0x0c/spltnrskb/docs/img/dial-study/dial-grid.jpg

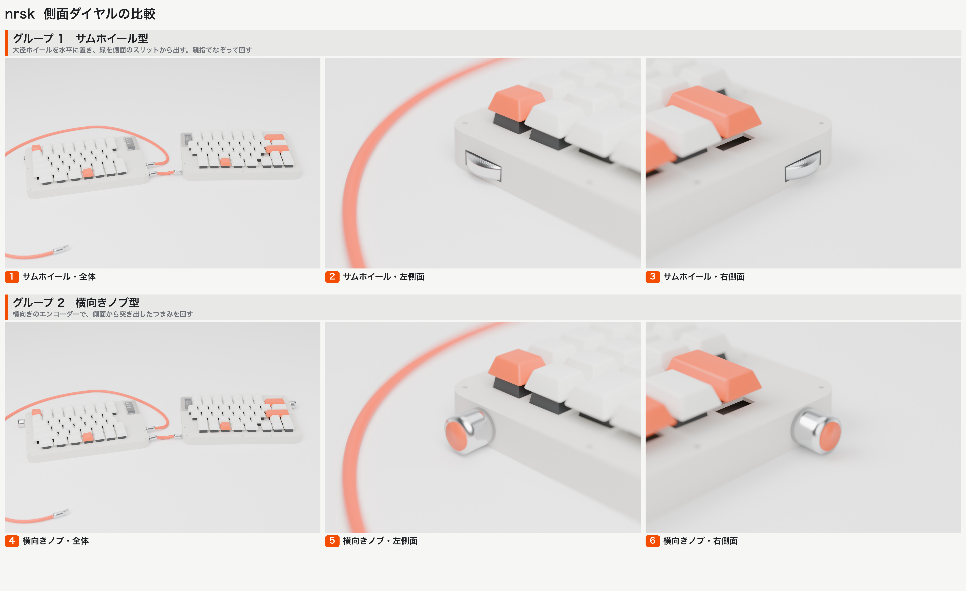
docs/img/dial-study/dial-grid.jpg
