0x0c/spltnrskb/docs/img/dial-study/dial-left-knob.png

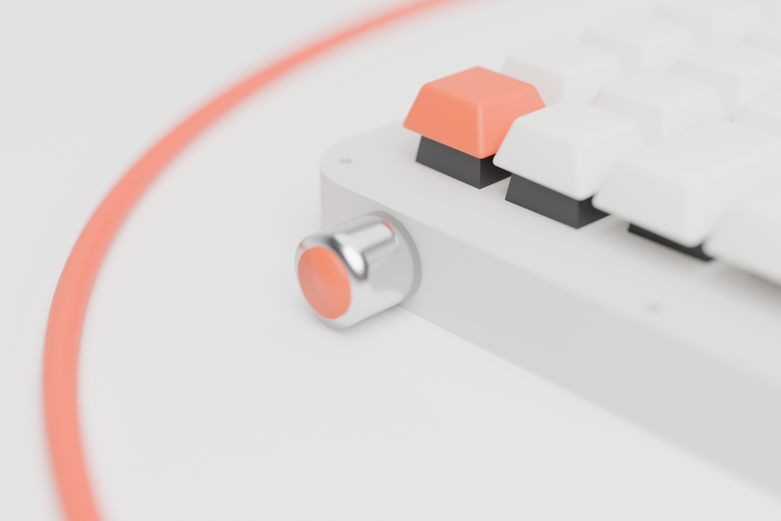
docs/img/dial-study/dial-left-knob.png
