0x0c/spltnrskb/docs/img/dial-study/dial-right-knob.png

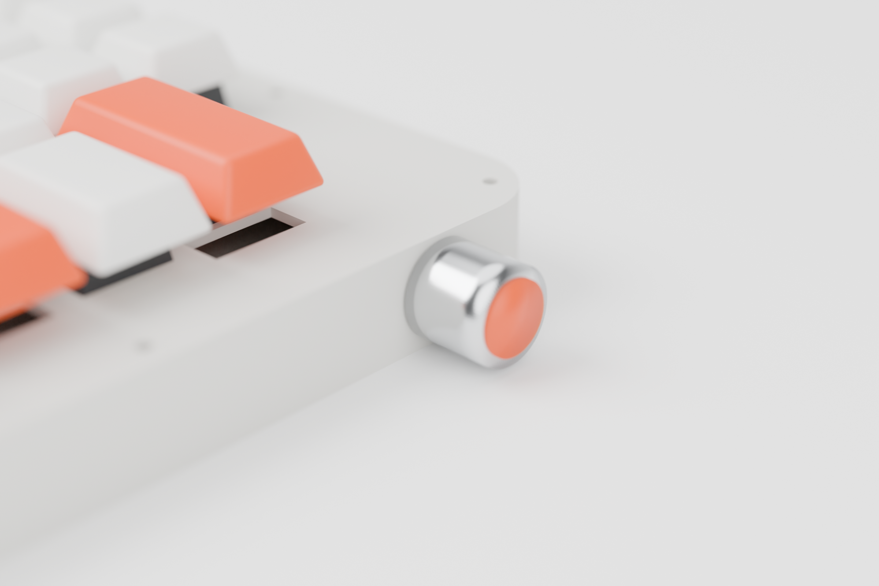
docs/img/dial-study/dial-right-knob.png
