0x0c/spltnrskb/docs/img/dial-study/hero-knob.png

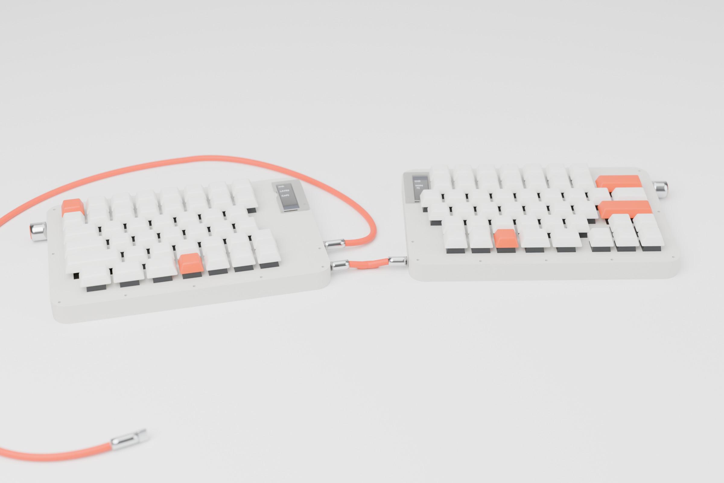
docs/img/dial-study/hero-knob.png
