0x0c/spltnrskb/docs/img/encoder-study/exploded-left.png

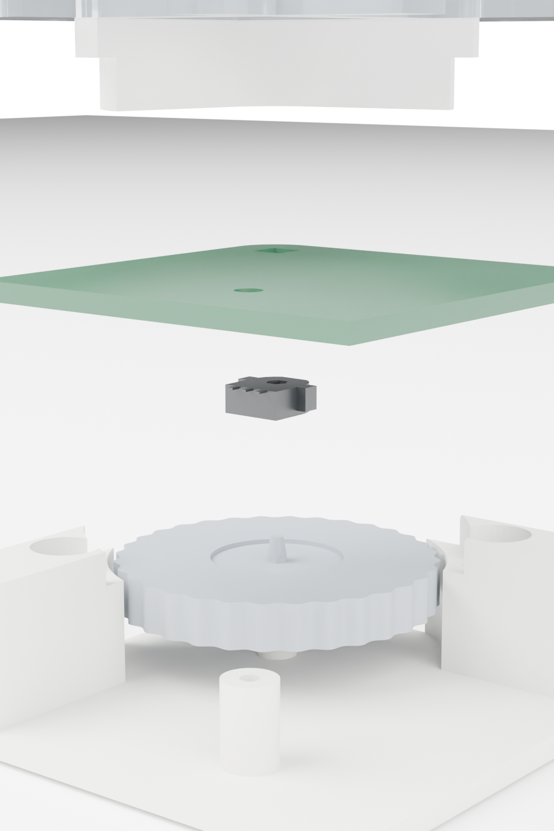
docs/img/encoder-study/exploded-left.png
