0x0c/spltnrskb/docs/img/encoder-study/exterior-right.png

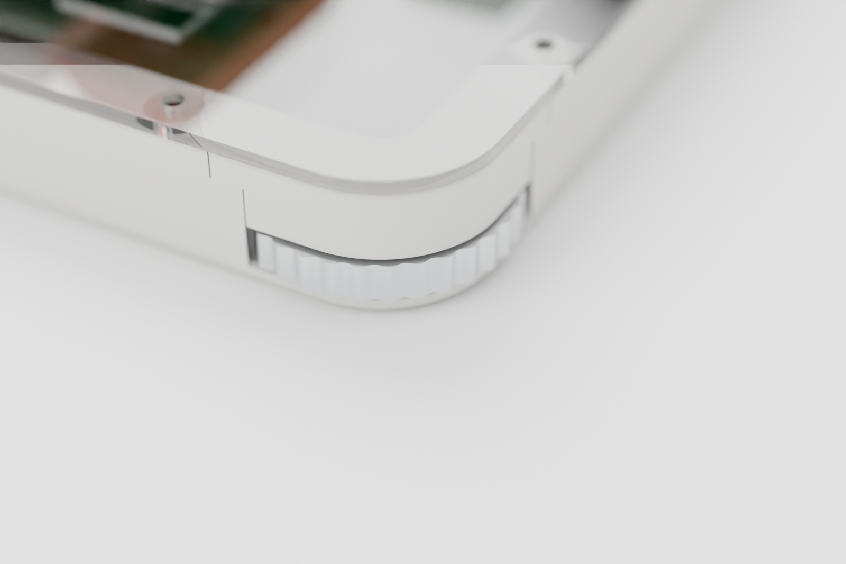
docs/img/encoder-study/exterior-right.png
