0x0c/spltnrskb/docs/img/encoder-study/section-left-encoder.png

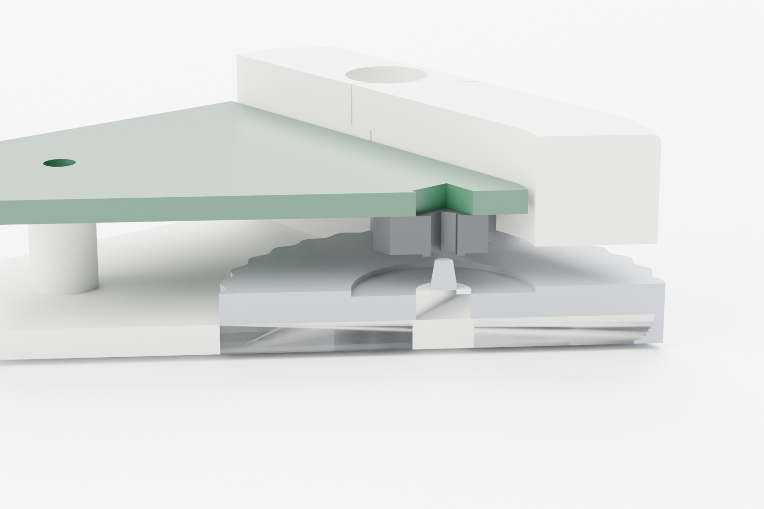
docs/img/encoder-study/section-left-encoder.png
