0x0c/spltnrskb/docs/img/oled-study/close-0.png

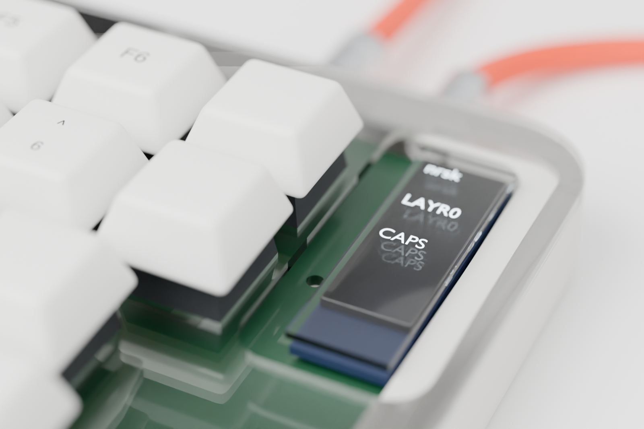
docs/img/oled-study/close-0.png
