0x0c/spltnrskb/docs/img/oled-study/close-3.5.png

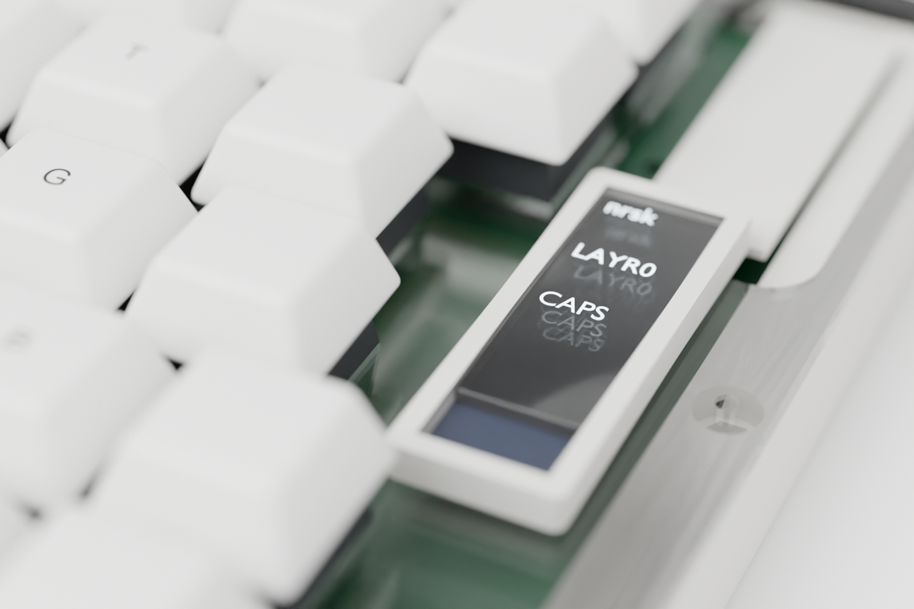
docs/img/oled-study/close-3.5.png
