0x0c/spltnrskb/docs/img/oled-study/close-13.png

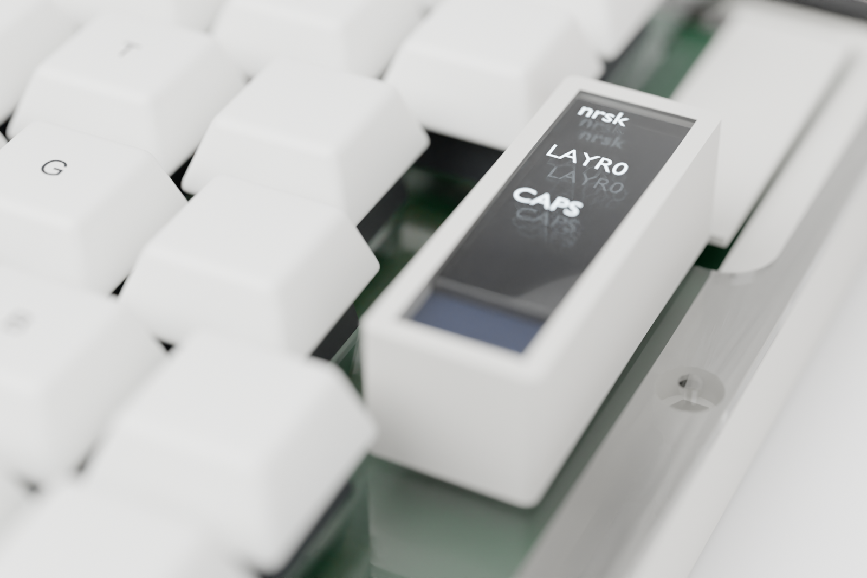
docs/img/oled-study/close-13.png
