0x0c/spltnrskb/docs/img/oled-study/close-tilt-h.png

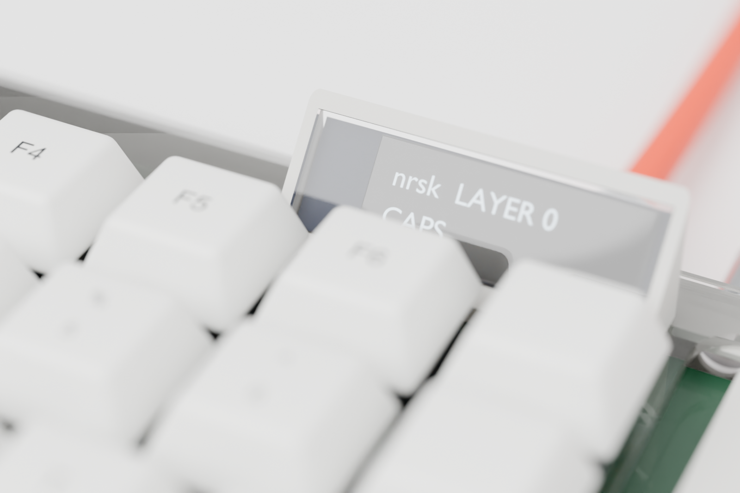
docs/img/oled-study/close-tilt-h.png
