0x0c/spltnrskb/docs/img/oled-study/close-tilt-v.png

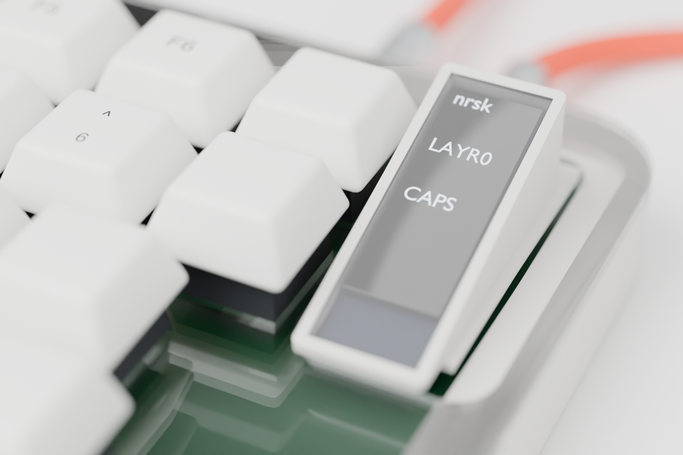
docs/img/oled-study/close-tilt-v.png
