0x0c/spltnrskb/docs/img/oled-study/user-0.png

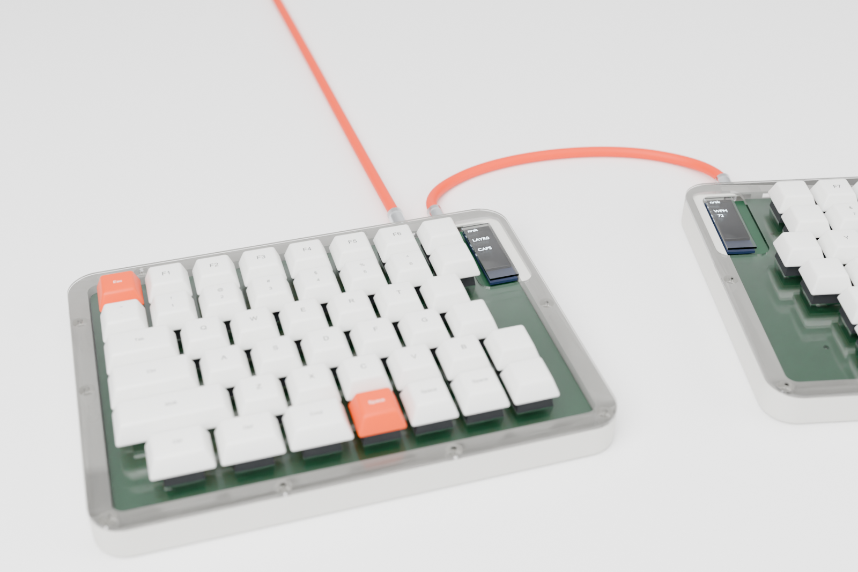
docs/img/oled-study/user-0.png
