0x0c/spltnrskb/docs/img/oled-study/user-tilt-h.png

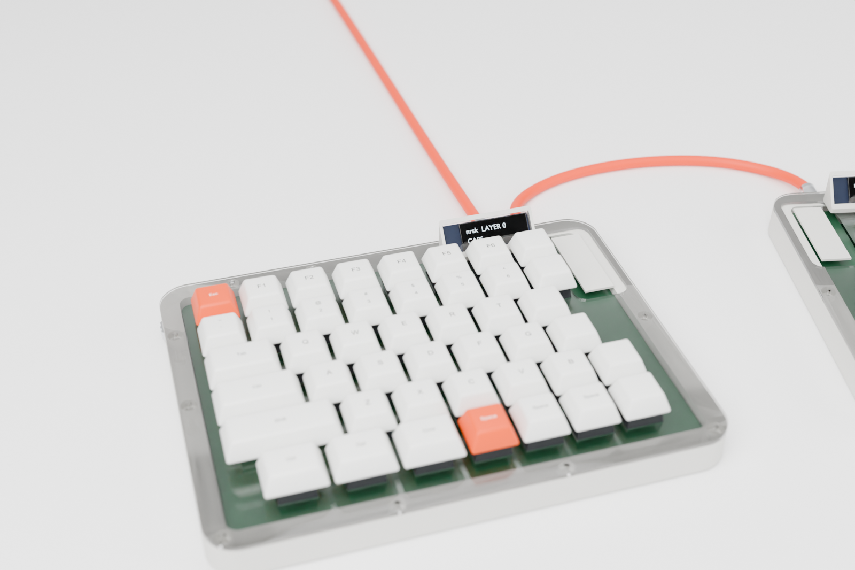
docs/img/oled-study/user-tilt-h.png
