0x0c/spltnrskb/docs/img/oled-study/user-tilt-v.png

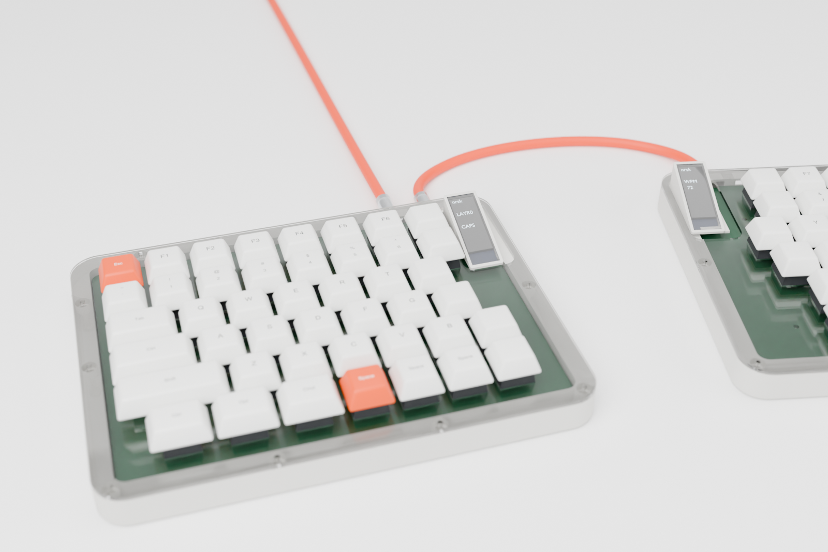
docs/img/oled-study/user-tilt-v.png
