0x0c/spltnrskb/docs/img/ports-compare.jpg

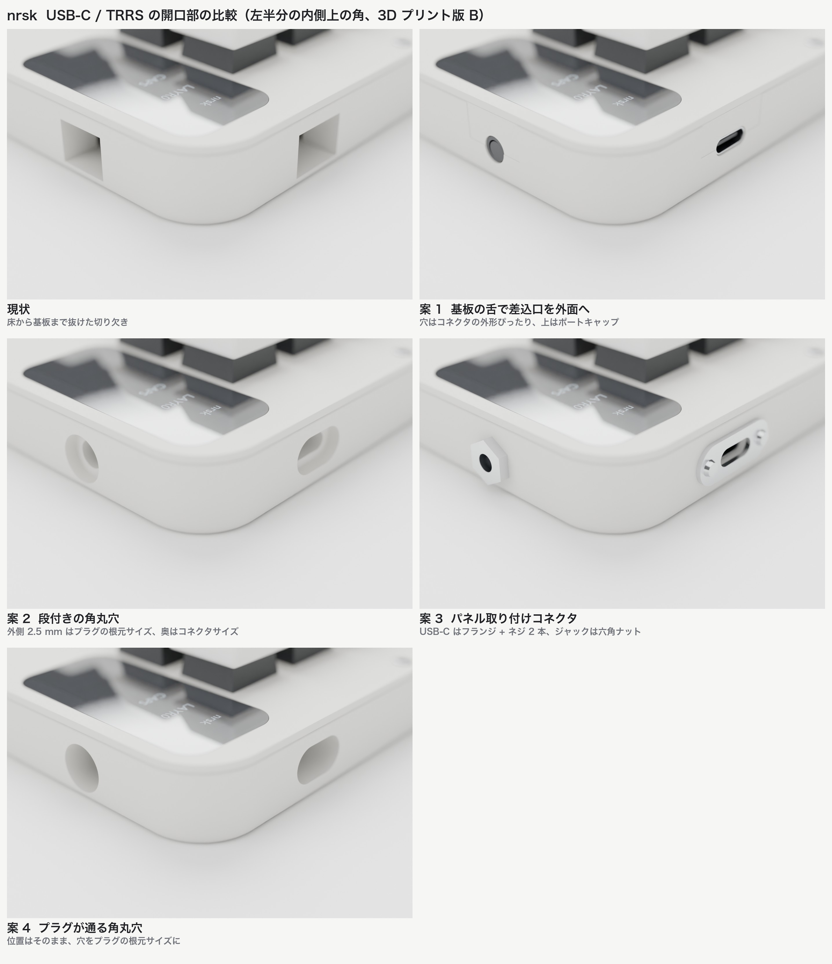
docs/img/ports-compare.jpg
