0x0c/spltnrskb/docs/img/render-detail.png

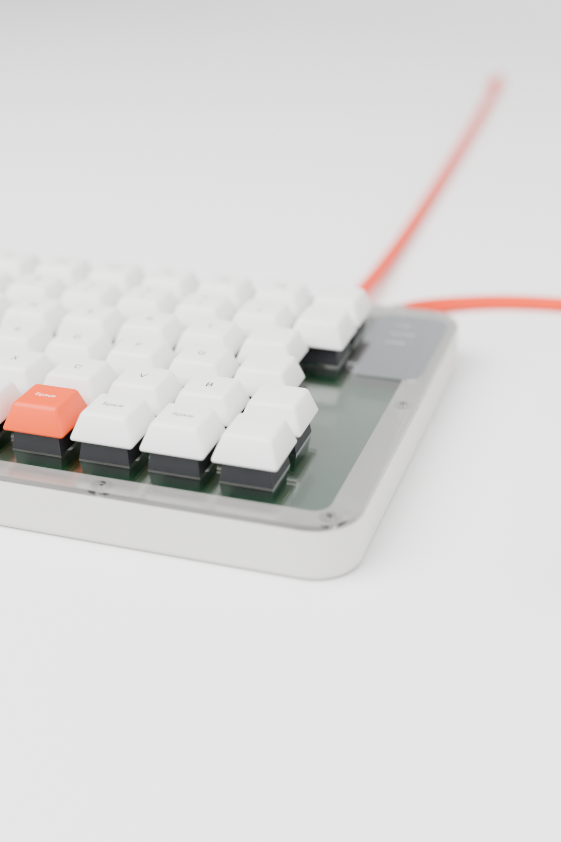
docs/img/render-detail.png
