0x0c/spltnrskb/docs/img/render-grid.jpg

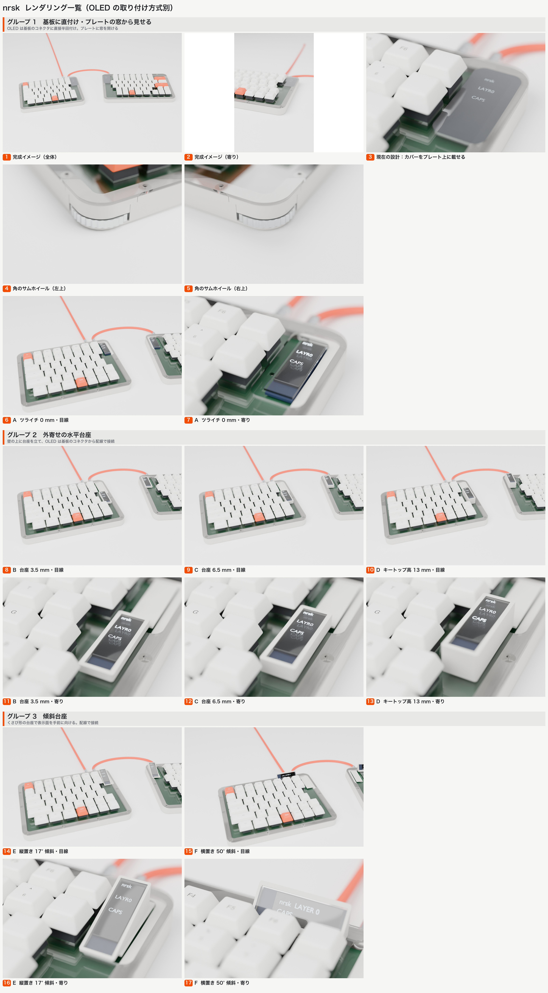
docs/img/render-grid.jpg
