0x0c/spltnrskb/docs/img/render-hero-top-acrylic-flat.png

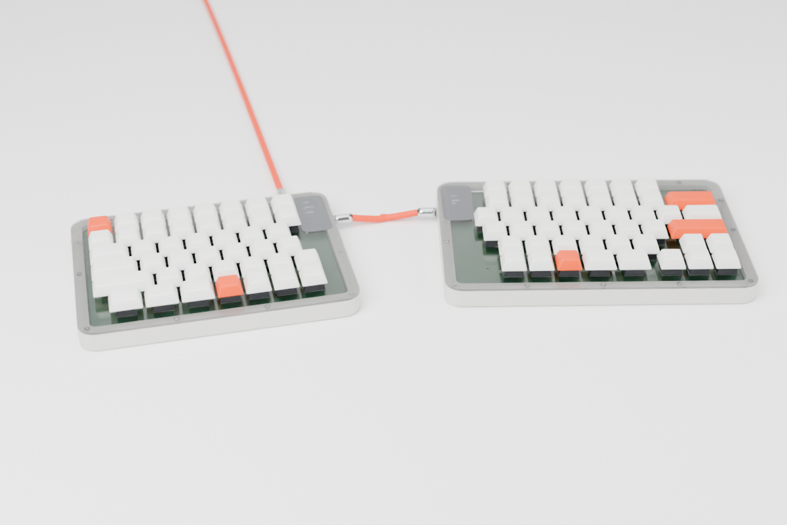
docs/img/render-hero-top-acrylic-flat.png
