0x0c/spltnrskb/docs/img/render-oled-top-acrylic-flat.png

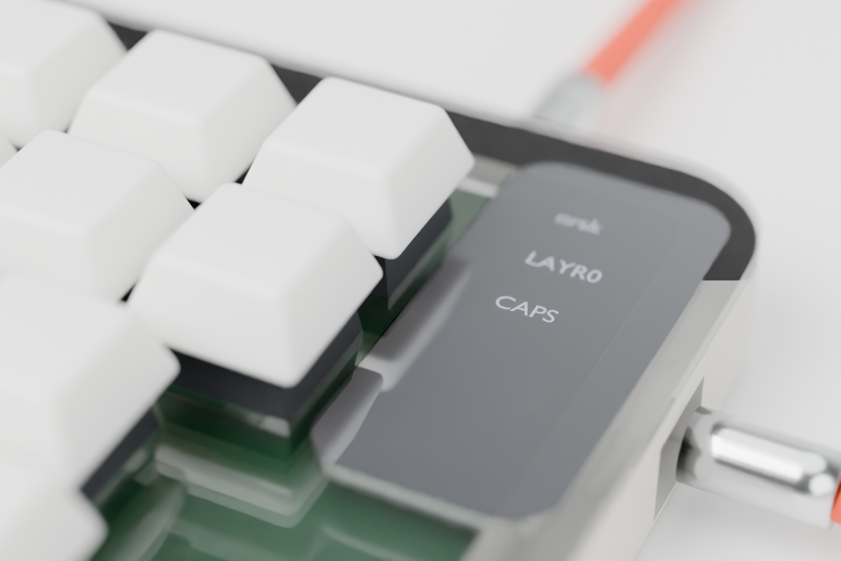
docs/img/render-oled-top-acrylic-flat.png
