0x0c/spltnrskb/docs/img/render-oled-top-acrylic-lowpan.png

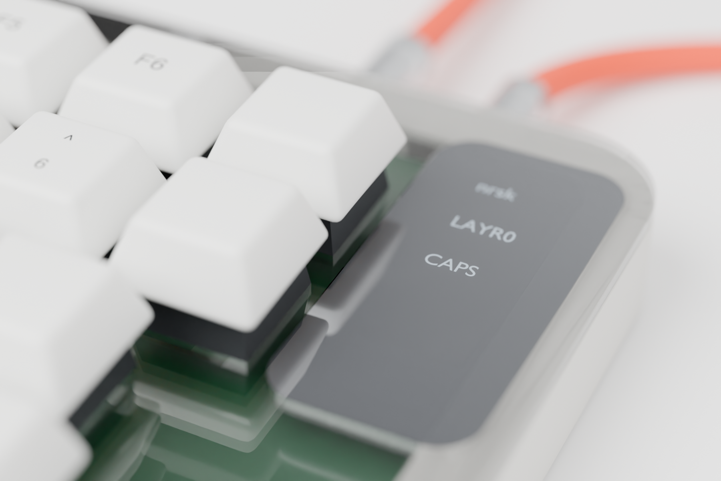
docs/img/render-oled-top-acrylic-lowpan.png
