0x0c/spltnrskb/docs/img/render-ports-current.png

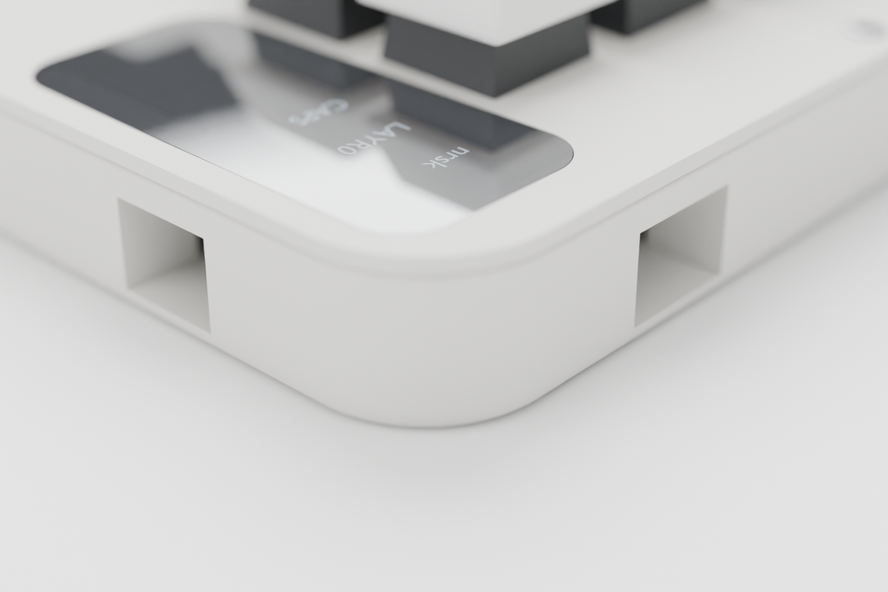
docs/img/render-ports-current.png
