0x0c/spltnrskb/docs/img/right-case-overlay.png

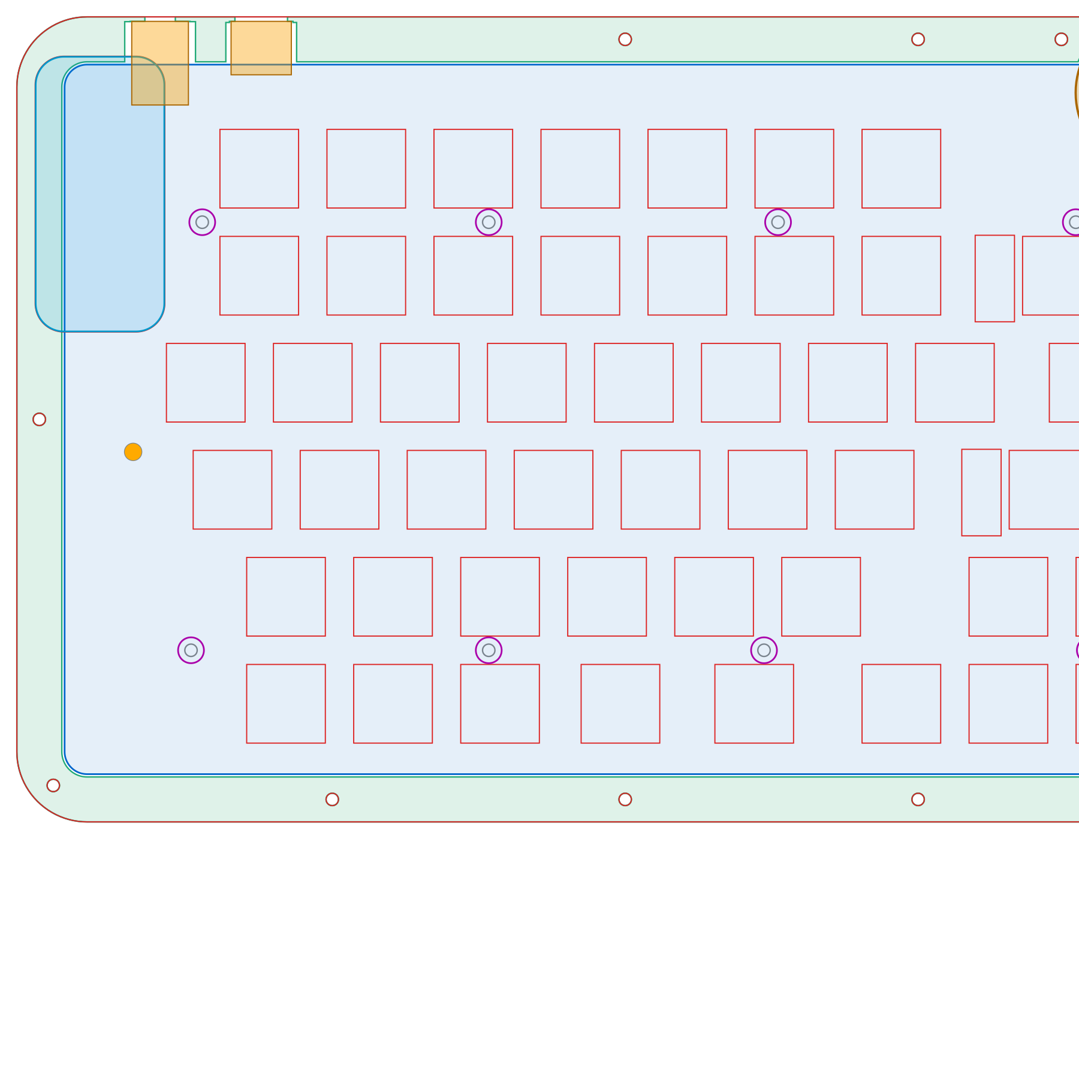
docs/img/right-case-overlay.png
