0x0c/spltnrskb/case/laser/left-frame3.dxf

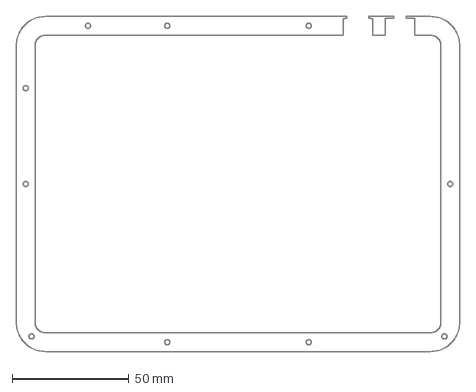
[picture p52: CAD file, 2026-10-10]
case/laser/left-frame3.dxf
189.6 x 143.3 mm
