0x0c/spltnrskb/case/preview/oled-variants/right-lens-tilt-h.stl

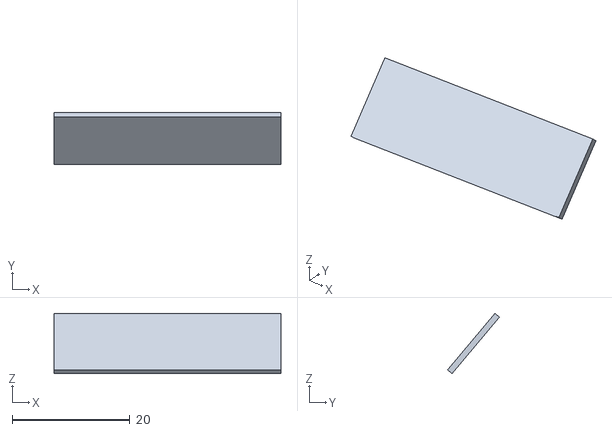
[picture p53: CAD file, 2026-10-04]
case/preview/oled-variants/right-lens-tilt-h.stl
38.5 x 8.80 x 10.2
