0x0c/spltnrskb/case/preview/port-variants/left-panel-heads.stl

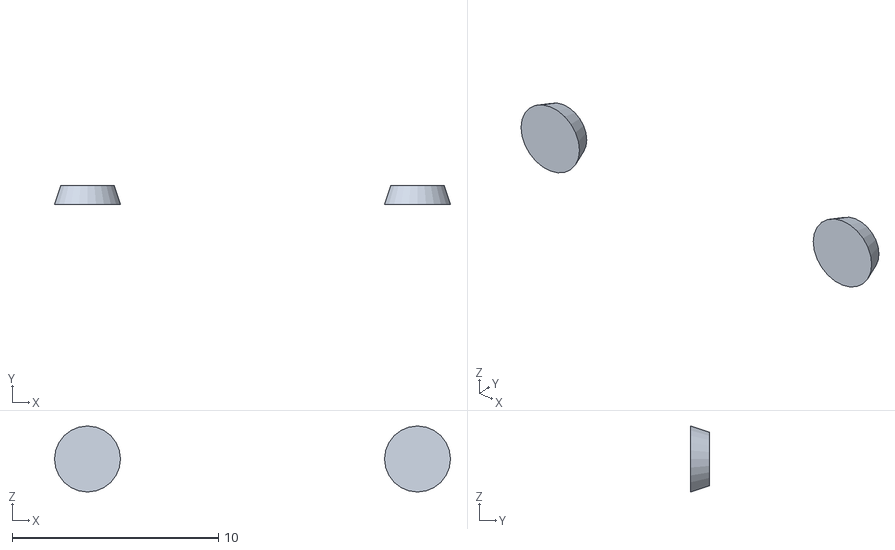
[picture p54: CAD file, 2026-10-05]
case/preview/port-variants/left-panel-heads.stl
19.2 x 0.9 x 3.20
