0x0c/spltnrskb/case/preview/right-pcb.stl

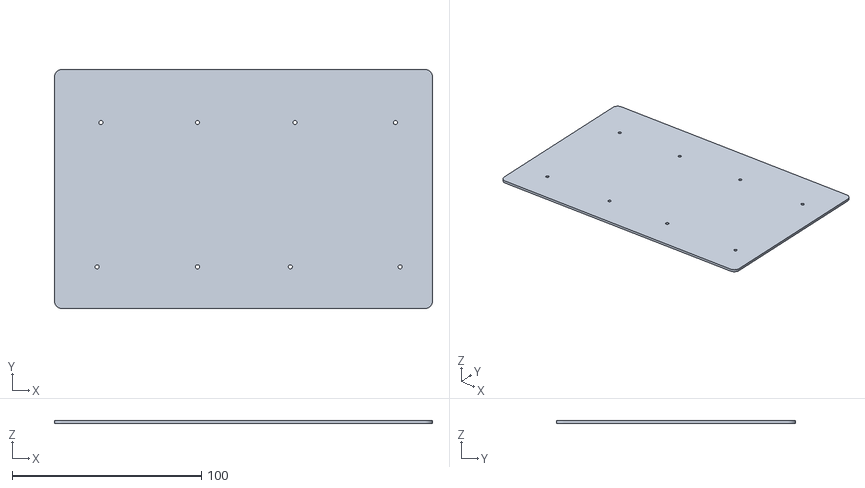
[picture p55: CAD file, 2026-10-10]
case/preview/right-pcb.stl
199.6 x 126.3 x 1.60
