0x0c/spltnrskb/case/print/left-tray.stl

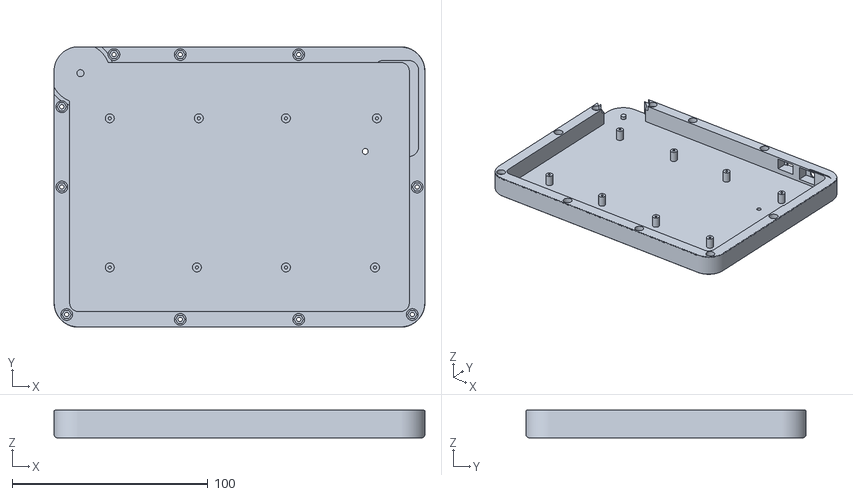
[picture p56: CAD file, 2026-10-10]
case/print/left-tray.stl
189.6 x 143.3 x 14.1
