0x0c/spltnrskb/case/laser/left-frame2.dxf

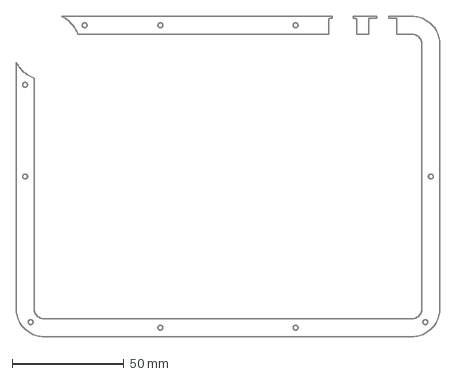
[picture p57: CAD file, 2026-10-10]
case/laser/left-frame2.dxf
189.6 x 143.3 mm
