0x0c/spltnrskb/case/preview/left-oled-cover.stl

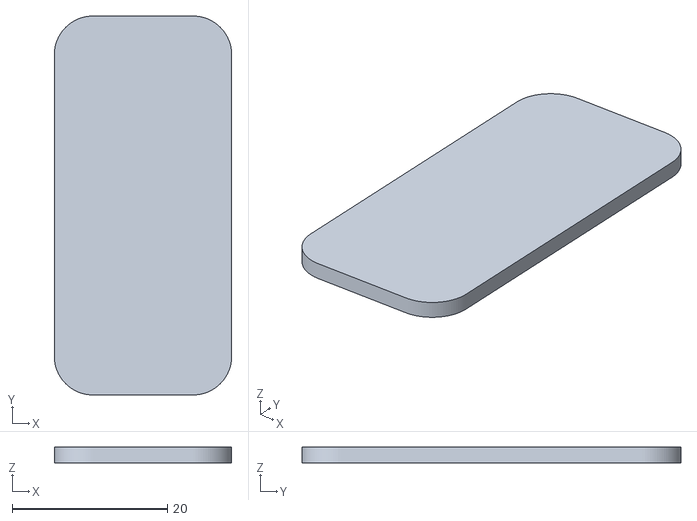
[picture p58: CAD file, 2026-10-05]
case/preview/left-oled-cover.stl
22.9 x 48.9 x 2.00
