0x0c/spltnrskb/case/preview/oled-variants/left-lens-tilt-v.stl

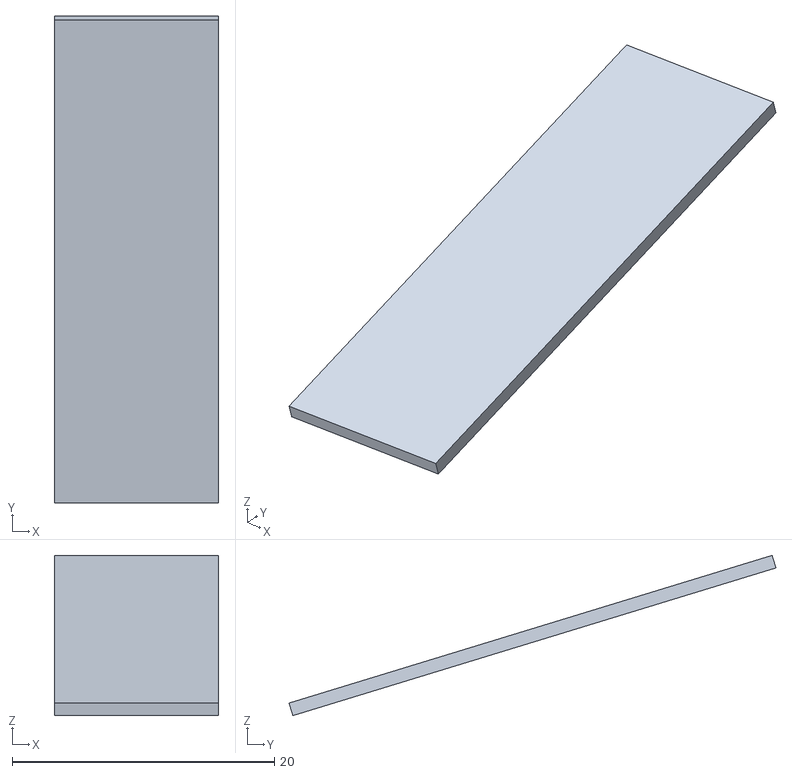
[picture p59: CAD file, 2026-10-04]
case/preview/oled-variants/left-lens-tilt-v.stl
12.5 x 37.1 x 12.2
