0x0c/spltnrskb/case/print/right-plate.stl

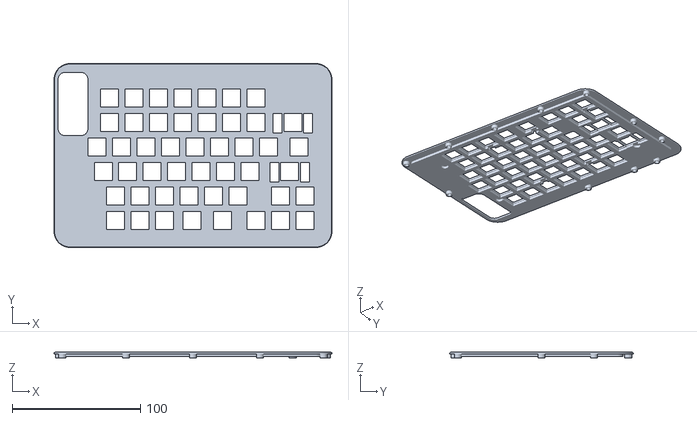
[picture p60: CAD file, 2026-10-10]
case/print/right-plate.stl
216.6 x 143.3 x 4.50
