0x0c/spltnrskb/case/laser/right-plate.dxf

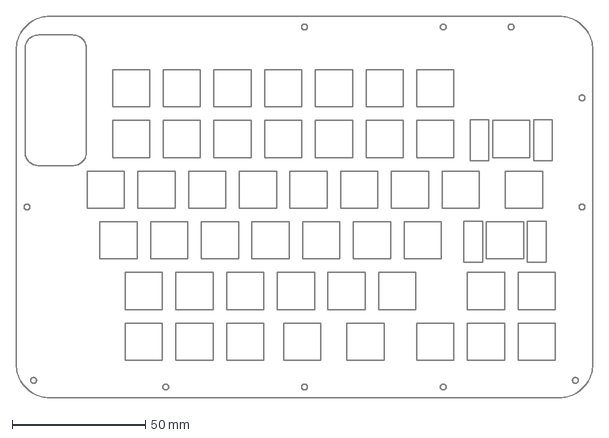
[picture p61: CAD file, 2026-10-10]
case/laser/right-plate.dxf
216.6 x 143.3 mm
