0x0c/spltnrskb/case/preview/oled-variants/left-lens-13.stl

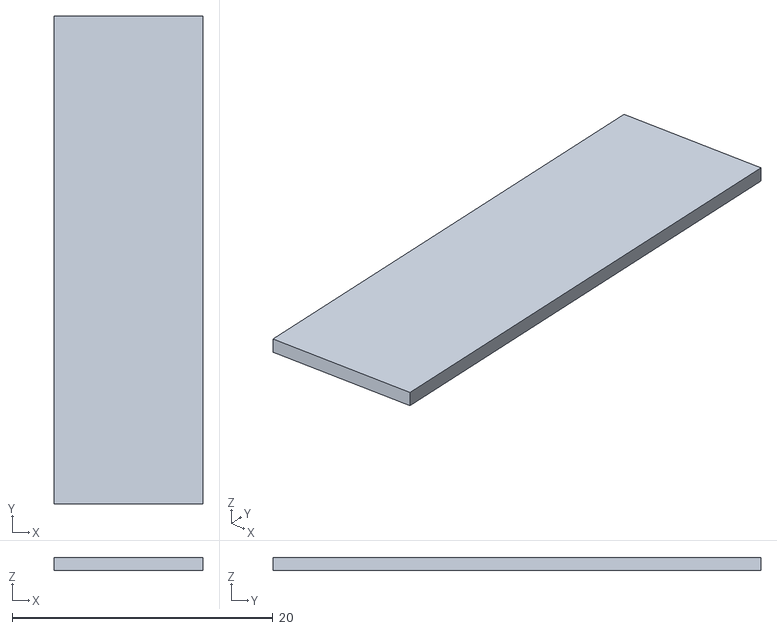
[picture p62: CAD file, 2026-10-04]
case/preview/oled-variants/left-lens-13.stl
11.4 x 37.4 x 1.00
