0x0c/spltnrskb/case/laser/left-frame1.dxf

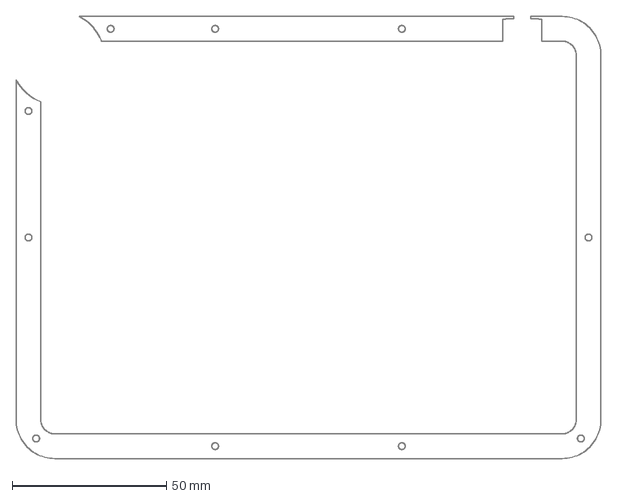
[picture p63: CAD file, 2026-10-10]
case/laser/left-frame1.dxf
189.6 x 143.3 mm
