0x0c/spltnrskb/case/preview/oled-variants/left-pod-6.5.stl

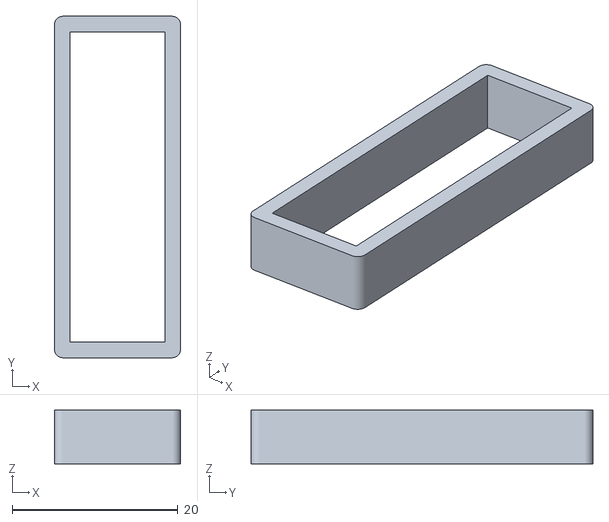
[picture p64: CAD file, 2026-10-04]
case/preview/oled-variants/left-pod-6.5.stl
15.2 x 41.2 x 6.50
