0x0c/spltnrskb/case/preview/port-variants/left-flush-jack.stl

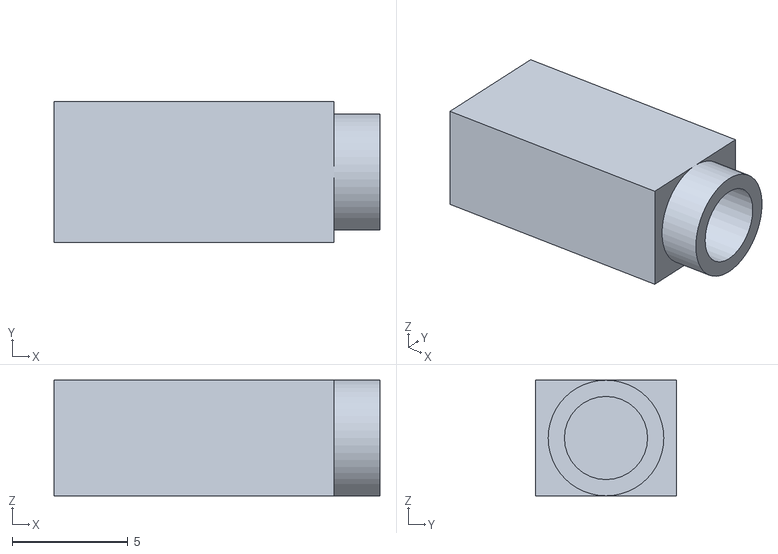
[picture p65: CAD file, 2026-10-05]
case/preview/port-variants/left-flush-jack.stl
14.1 x 6.10 x 5.00
