0x0c/spltnrskb/case/laser/left-bottom.dxf

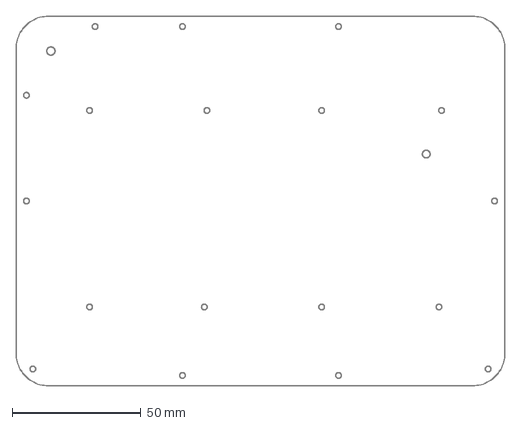
[picture p66: CAD file, 2026-10-10]
case/laser/left-bottom.dxf
189.6 x 143.3 mm
