0x0c/spltnrskb/case/preview/port-variants/left-flush-bore.stl

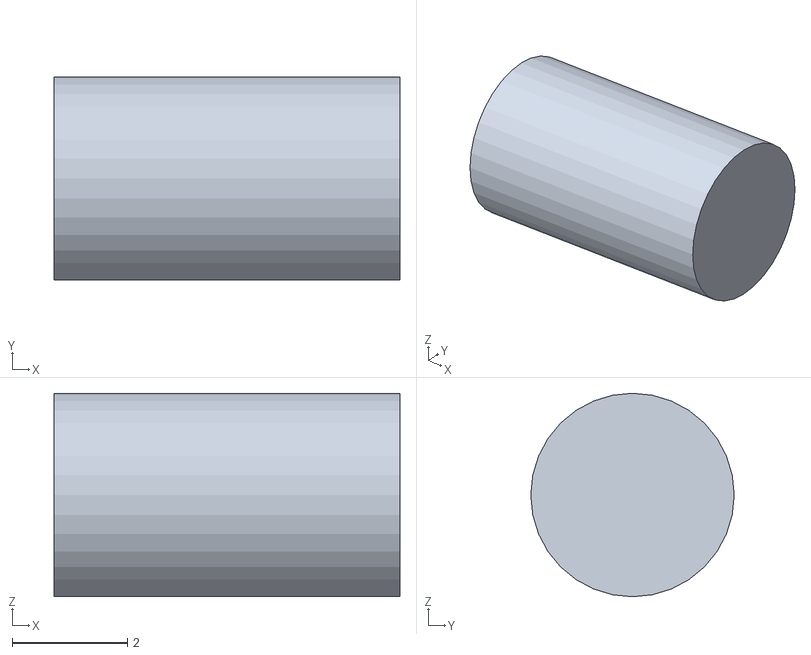
[picture p67: CAD file, 2026-10-05]
case/preview/port-variants/left-flush-bore.stl
6.00 x 3.53 x 3.53
