0x0c/spltnrskb/case/print/left-plate.stl

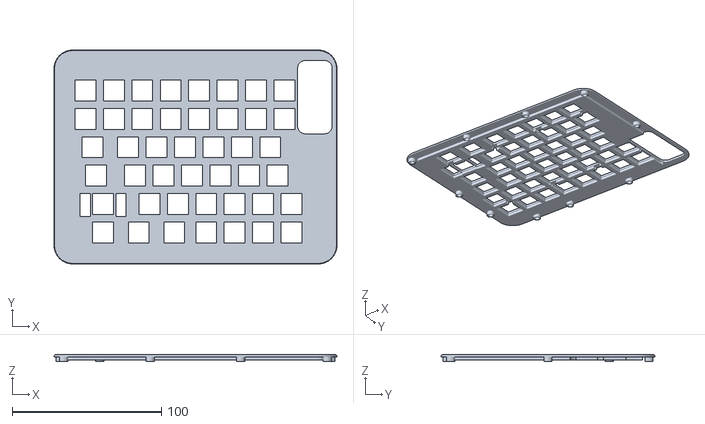
[picture p68: CAD file, 2026-10-10]
case/print/left-plate.stl
189.6 x 143.3 x 4.50
