0x0c/spltnrskb/case/laser/left-plate.dxf

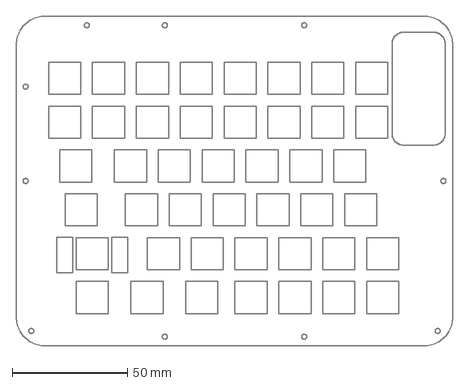
[picture p69: CAD file, 2026-10-10]
case/laser/left-plate.dxf
189.6 x 143.3 mm
