0x0c/spltnrskb/case/preview/port-variants/left-flush-shell.stl

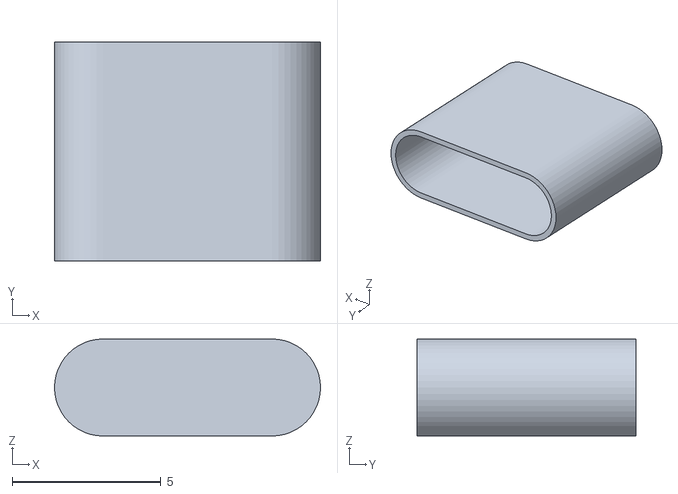
[picture p70: CAD file, 2026-10-05]
case/preview/port-variants/left-flush-shell.stl
8.94 x 7.35 x 3.26
