0x0c/spltnrskb/case/print/pin-coupon.stl

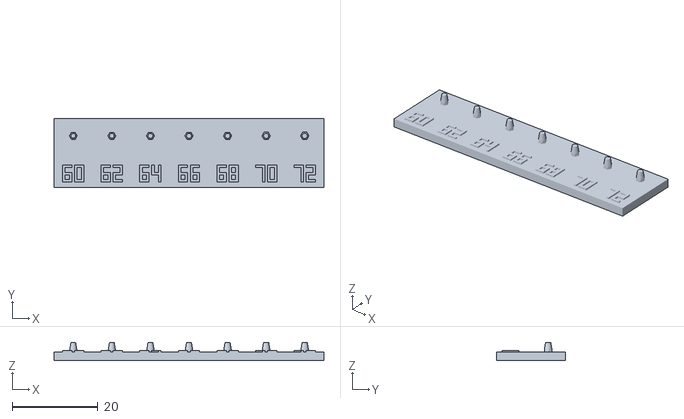
[picture p71: CAD file, 2026-10-10]
case/print/pin-coupon.stl
63.0 x 16.0 x 4.30
