0x0c/spltnrskb/case/laser/right-frame2.dxf

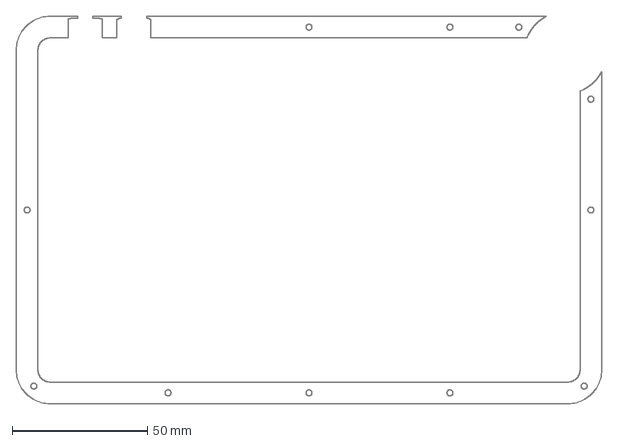
[picture p72: CAD file, 2026-10-10]
case/laser/right-frame2.dxf
216.6 x 143.3 mm
