0x0c/spltnrskb/case/laser/right-frame4.dxf

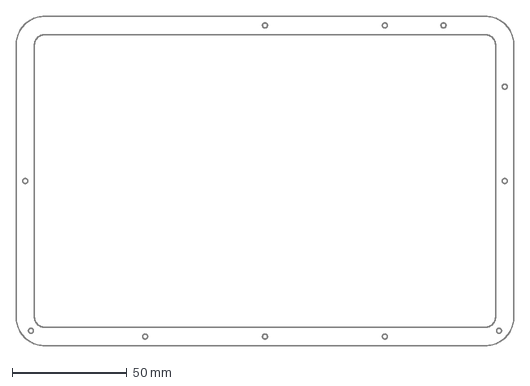
[picture p73: CAD file, 2026-10-10]
case/laser/right-frame4.dxf
216.6 x 143.3 mm
