0x0c/spltnrskb/case/preview/oled-variants/right-pod-tilt-h.stl

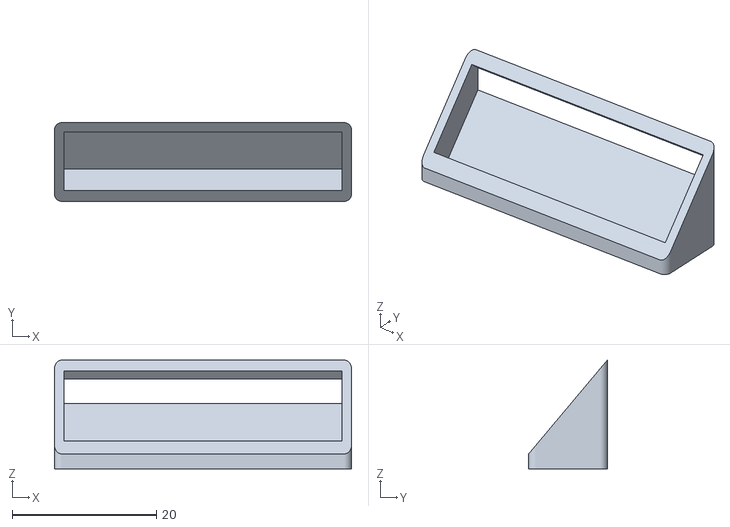
[picture p74: CAD file, 2026-10-04]
case/preview/oled-variants/right-pod-tilt-h.stl
41.2 x 10.9 x 15.1
