0x0c/spltnrskb/case/laser/right-frame1.dxf

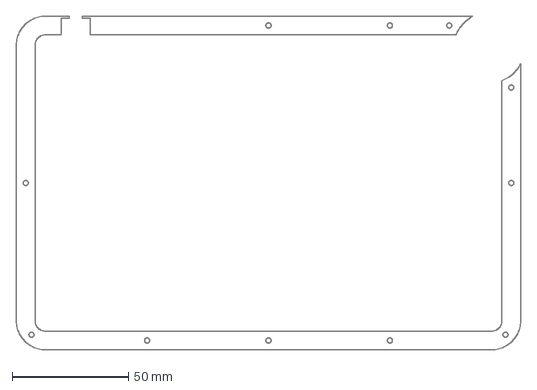
[picture p75: CAD file, 2026-10-10]
case/laser/right-frame1.dxf
216.6 x 143.3 mm
