0x0c/spltnrskb/case/laser/right-oled-cover.dxf

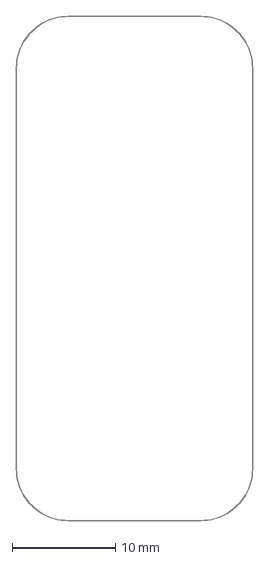
[picture p76: CAD file, 2026-10-05]
case/laser/right-oled-cover.dxf
22.9 x 48.9 mm
