0x0c/spltnrskb/case/preview/oled-variants/right-pod-tilt-v.stl

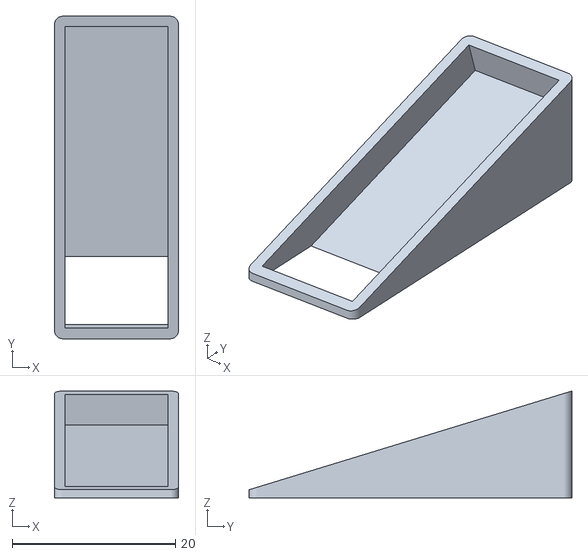
[picture p77: CAD file, 2026-10-04]
case/preview/oled-variants/right-pod-tilt-v.stl
15.2 x 39.5 x 13.1
