0x0c/spltnrskb/case/laser/left-oled-cover.dxf

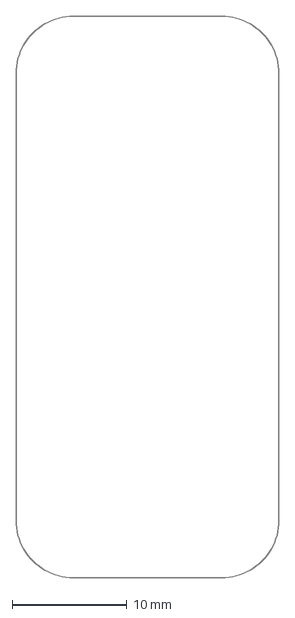
[picture p78: CAD file, 2026-10-05]
case/laser/left-oled-cover.dxf
22.9 x 48.9 mm
