0x0c/spltnrskb/case/preview/oled-variants/right-pod-3.5.stl

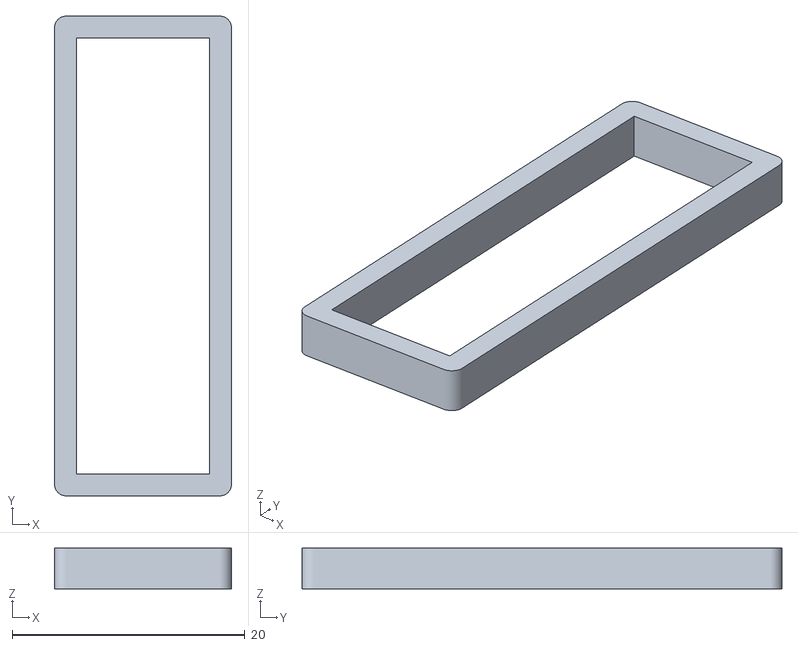
[picture p79: CAD file, 2026-10-04]
case/preview/oled-variants/right-pod-3.5.stl
15.2 x 41.2 x 3.50
