0x0c/spltnrskb/case/preview/port-variants/left-flush-cap.stl

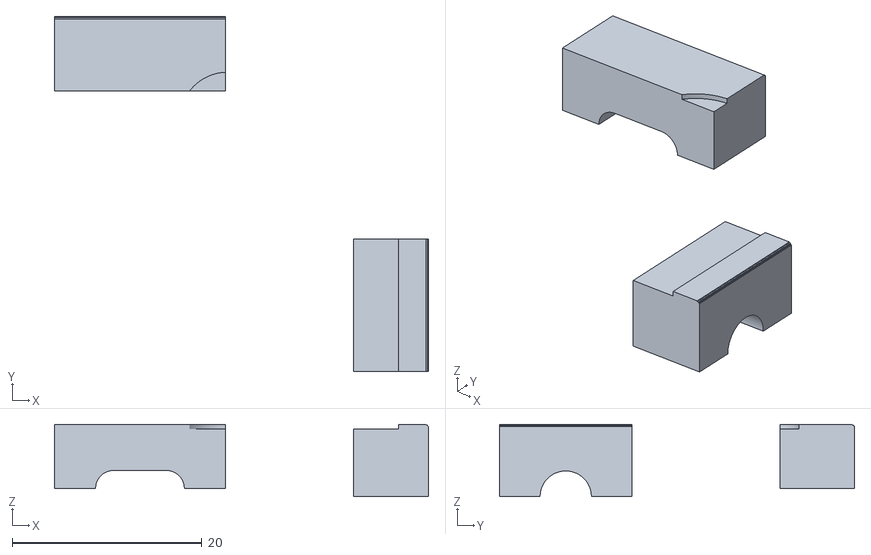
[picture p80: CAD file, 2026-10-05]
case/preview/port-variants/left-flush-cap.stl
39.4 x 37.4 x 7.60
