0x0c/spltnrskb/case/preview/port-variants/left-panel-tongue.stl

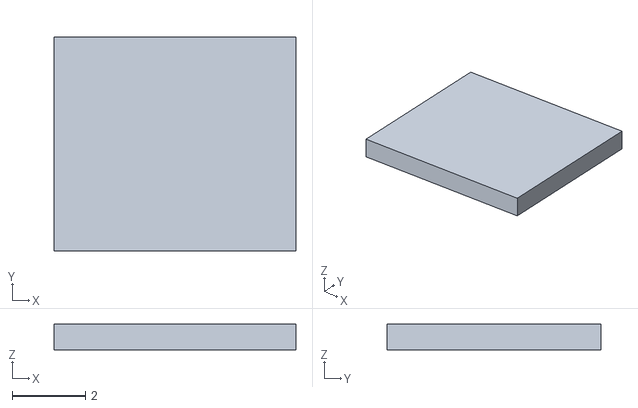
[picture p81: CAD file, 2026-10-05]
case/preview/port-variants/left-panel-tongue.stl
6.60 x 5.85 x 0.7
