0x0c/spltnrskb/docs/img/render-oled-top-print.png

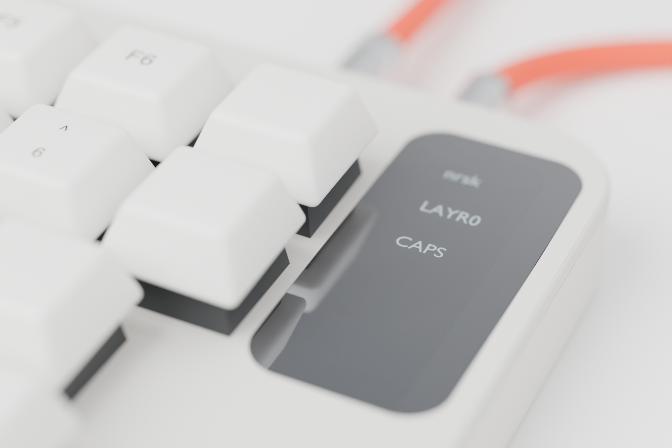
docs/img/render-oled-top-print.png
