0x0c/spltnrskb/docs/img/render-wheel-left-top-print-flat.png

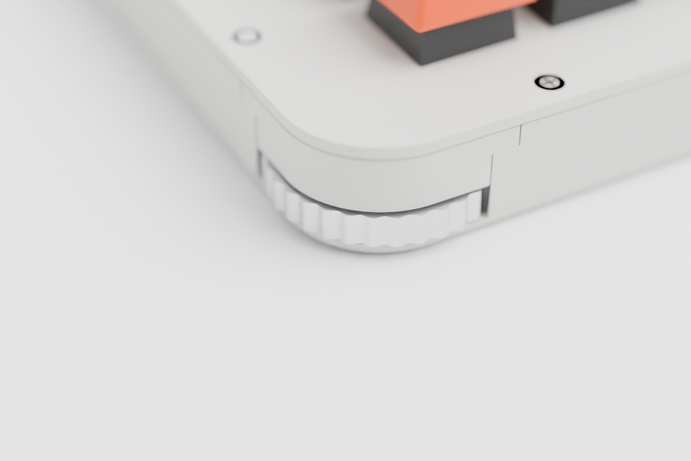
docs/img/render-wheel-left-top-print-flat.png
