0x0c/spltnrskb/gen/sexpr.py

"""Minimal S-expression reader/writer for KiCad files."""
import re

_tok = re.compile(r'\s*(?:(\()|(\))|("(?:[^"\\]|\\.)*")|([^\s()"]+))')


class Sym(str):
    """Unquoted atom."""


def parse(text):
    stack, cur = [], []
    pos = 0
    while True:
        m = _tok.match(text, pos)
        if not m or m.end() == pos:
            break
        pos = m.end()
        lp, rp, s, a = m.groups()
        if lp:
            stack.append(cur)
            cur = []
        elif rp:
            done = cur
            cur = stack.pop()
            cur.append(done)
        elif s is not None:
            cur.append(bytes(s[1:-1], 'utf-8').decode('unicode_escape') if '\\' in s else s[1:-1])
        else:
            cur.append(Sym(a))
    return cur[0]


def q(s):
    return '"' + str(s).replace('\\', '\\\\').replace('"', '\\"') + '"'


def dump(node, indent=0):
    if isinstance(node, list):
        if all(not isinstance(x, list) for x in node):
            return '(' + ' '.join(dump(x) for x in node) + ')'
        pad = '\t' * (indent + 1)
        parts = [dump(node[0])] if node else []
        out = '(' + ' '.join(dump(x) for x in node[:1])
        for x in node[1:]:
            if isinstance(x, list):
                out += '\n' + pad + dump(x, indent + 1)
            else:
                out += ' ' + dump(x)
        return out + '\n' + '\t' * indent + ')'
    if isinstance(node, Sym):
        return str(node)
    if isinstance(node, bool):
        return 'yes' if node else 'no'
    if isinstance(node, (int, float)):
        return fmt(node)
    return q(node)


def fmt(v):
    if isinstance(v, int):
        return str(v)
    s = f'{v:.4f}'.rstrip('0').rstrip('.')
    return '0' if s == '-0' else s


def find(node, key):
    return [x for x in node if isinstance(x, list) and x and x[0] == key]


def find1(node, key):
    r = find(node, key)
    return r[0] if r else None
